xueyouluo/fridge_tracker/models/ink_frame_v1/review/rear_shell_open_side_20260711T084902Z.png

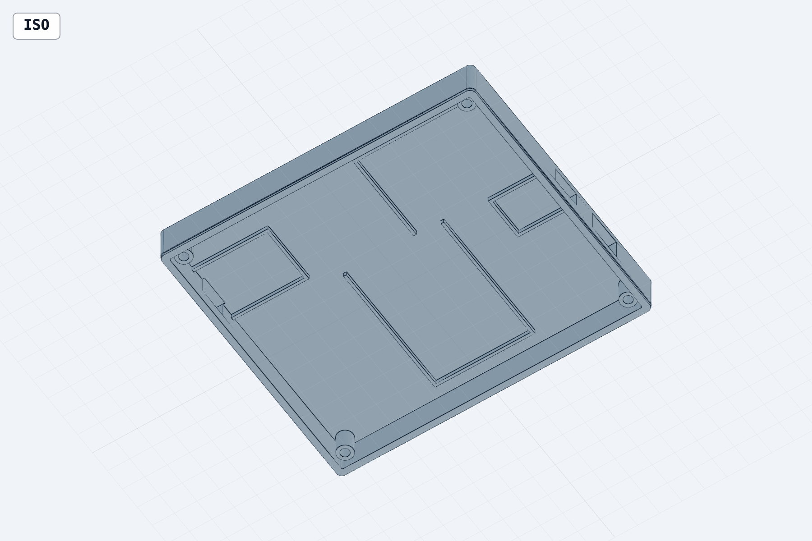
models/ink_frame_v1/review/rear_shell_open_side_20260711T084902Z.png
