xueyouluo/fridge_tracker/models/ink_frame_v1/review/assembly_front_20260710T135041Z.png

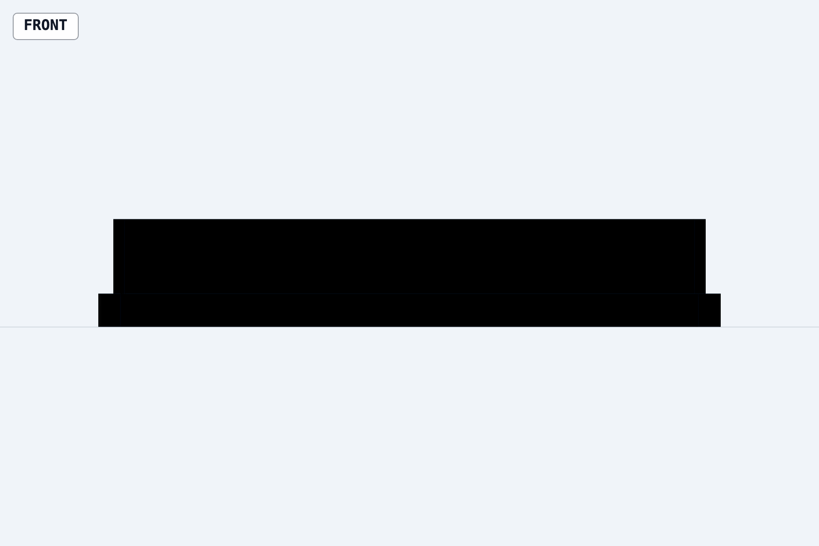
models/ink_frame_v1/review/assembly_front_20260710T135041Z.png
